mathieupommery/Keyring-GPSTRACKER/Docs/auxpcbside2.png

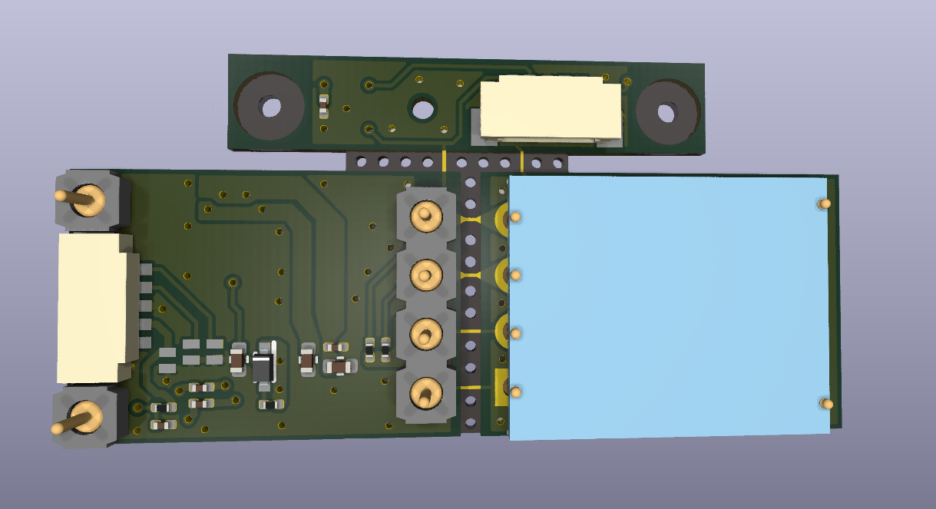
Docs/auxpcbside2.png
