mathieupommery/Keyring-GPSTRACKER/Docs/balise.jpeg

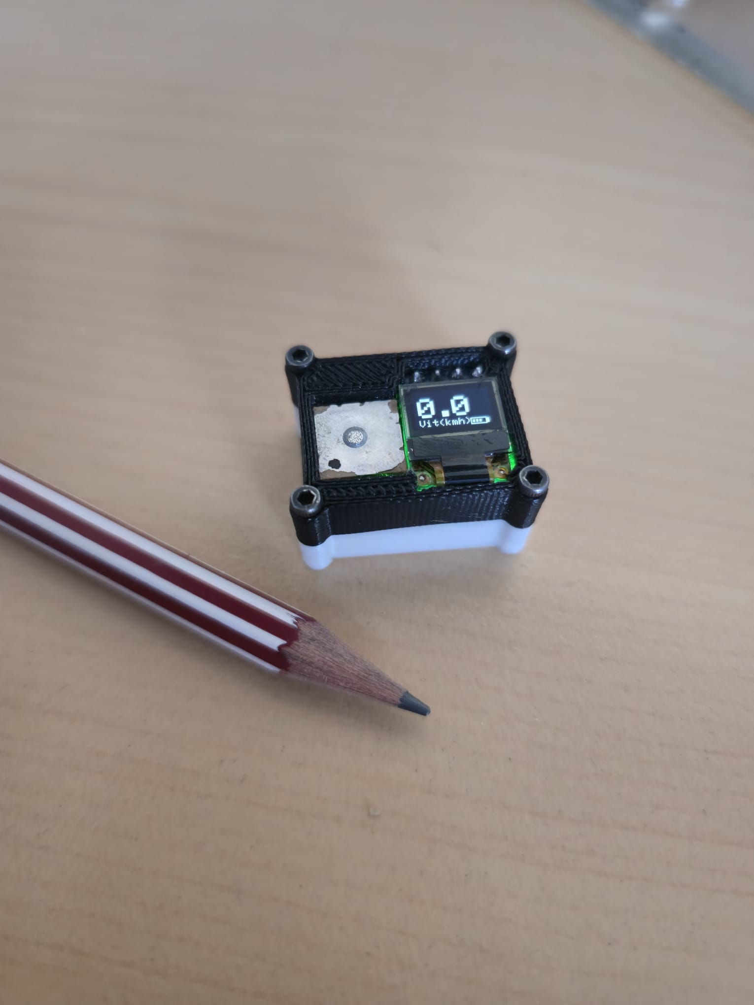
Docs/balise.jpeg
