mathieupommery/Keyring-GPSTRACKER/Docs/gpsbottom.png

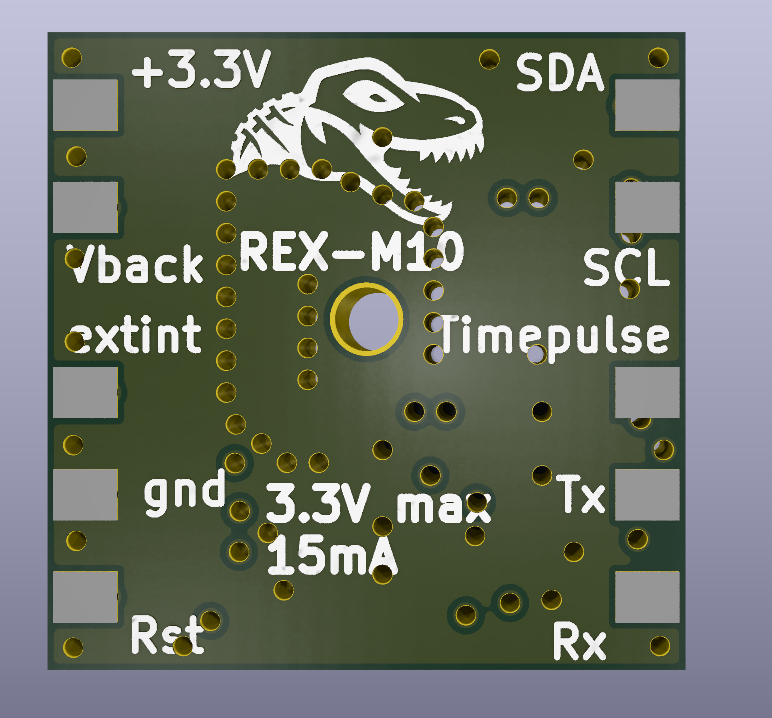
Docs/gpsbottom.png
