mathieupommery/Keyring-GPSTRACKER/Docs/rex_m10pcb.png

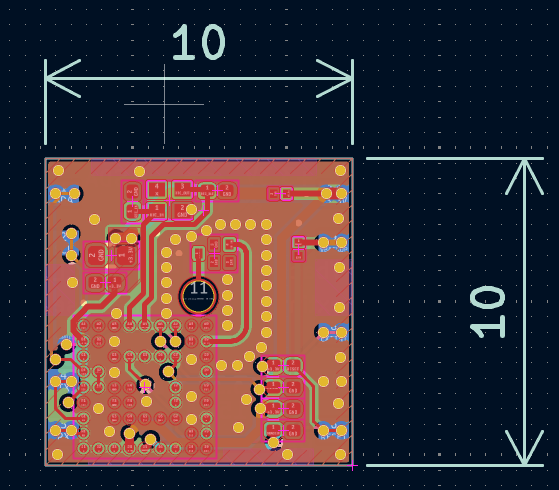
Docs/rex_m10pcb.png
