mathieupommery/Keyring-GPSTRACKER/Docs/v12back.png

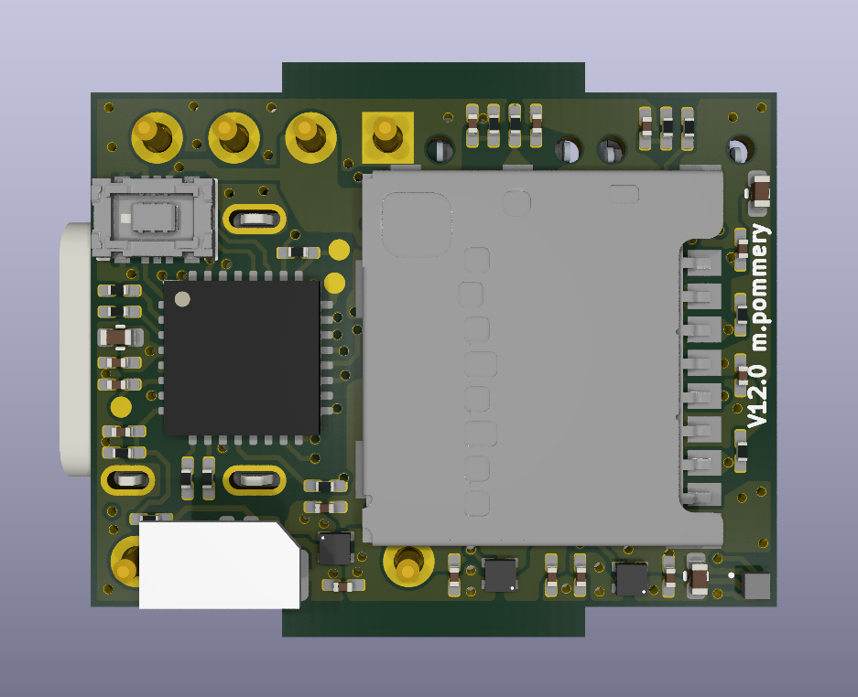
Docs/v12back.png
