mathieupommery/Keyring-GPSTRACKER/Docs/v12side.png

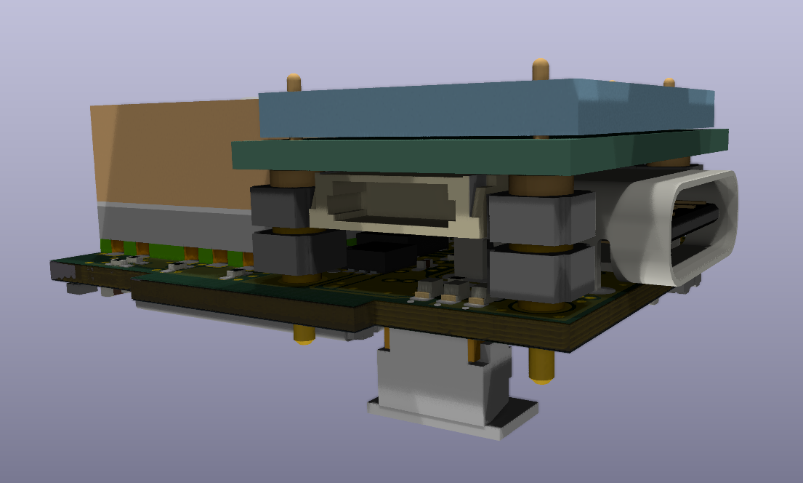
Docs/v12side.png
