mathieupommery/Keyring-GPSTRACKER/Docs/v12top.png

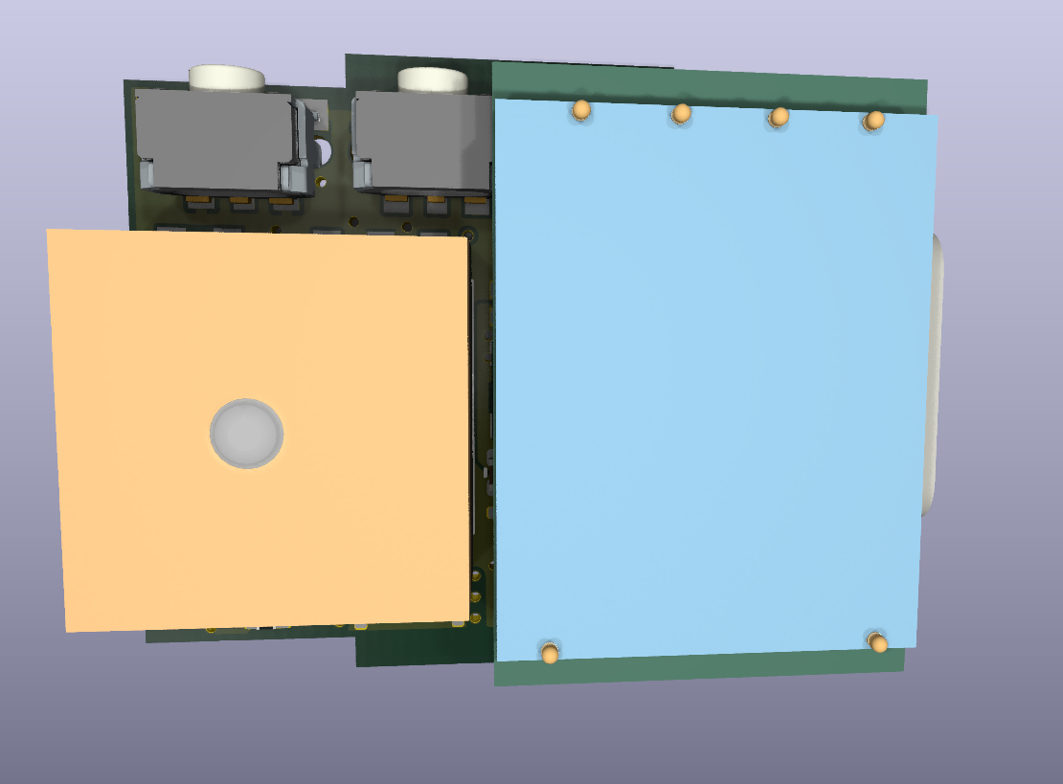
Docs/v12top.png
