mathieupommery/Keyring-GPSTRACKER/Docs/watercase1.png

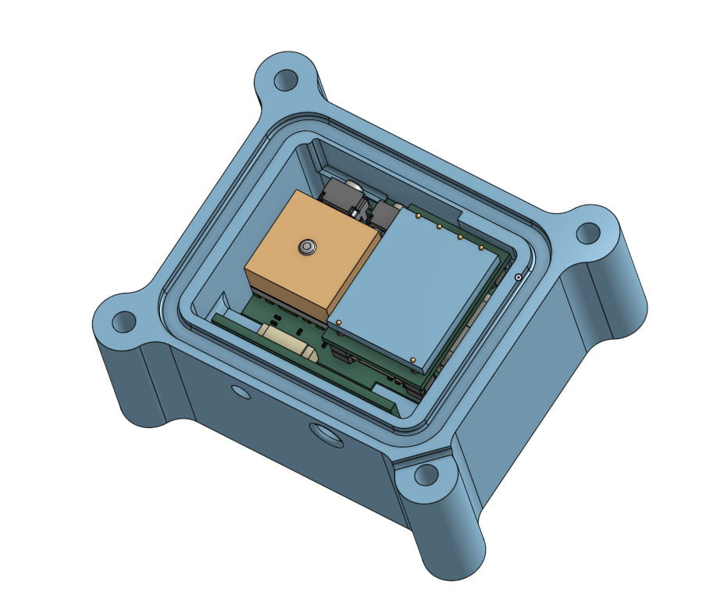
Docs/watercase1.png
