mathieupommery/Keyring-GPSTRACKER/Hardware/3d schématic/composant/BM06B-SURS-TF-LF--SN---3DModel-STEP-56544.STEP

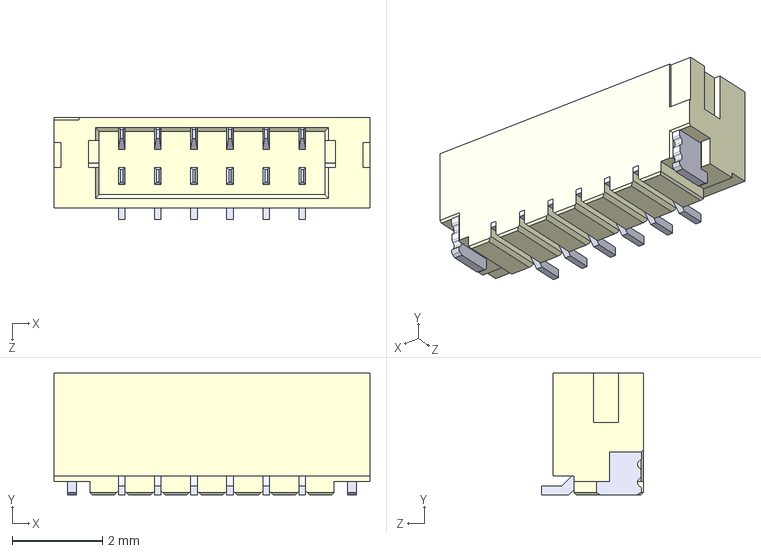
[picture p29: CAD file, 2026-07-01]
Hardware/3d schématic/composant/BM06B-SURS-TF-LF--SN---3DModel-STEP-56544.STEP
7.00 x 2.70 x 2.25 mm
