mathieupommery/Keyring-GPSTRACKER/Hardware/3d schématic/composant/0.42inch.step

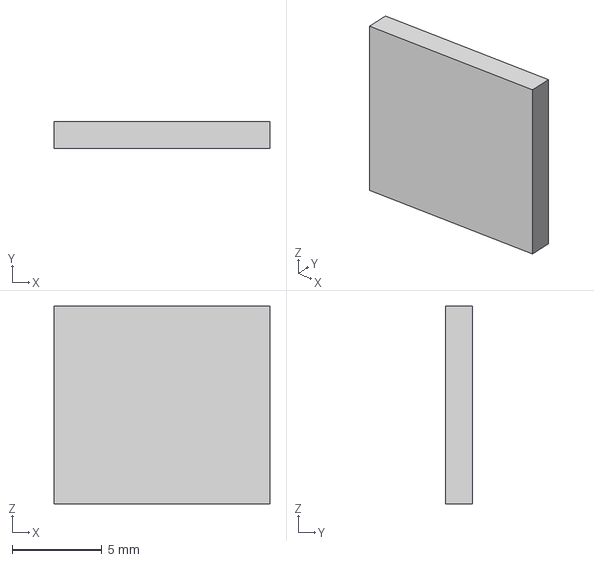
[picture p30: CAD file, 2026-07-01]
Hardware/3d schématic/composant/0.42inch.step
12.0 x 1.50 x 11.0 mm
