mathieupommery/Keyring-GPSTRACKER/Hardware/3d schématic/composant/CD-PA1010D--3DModel-STEP-271329.STEP

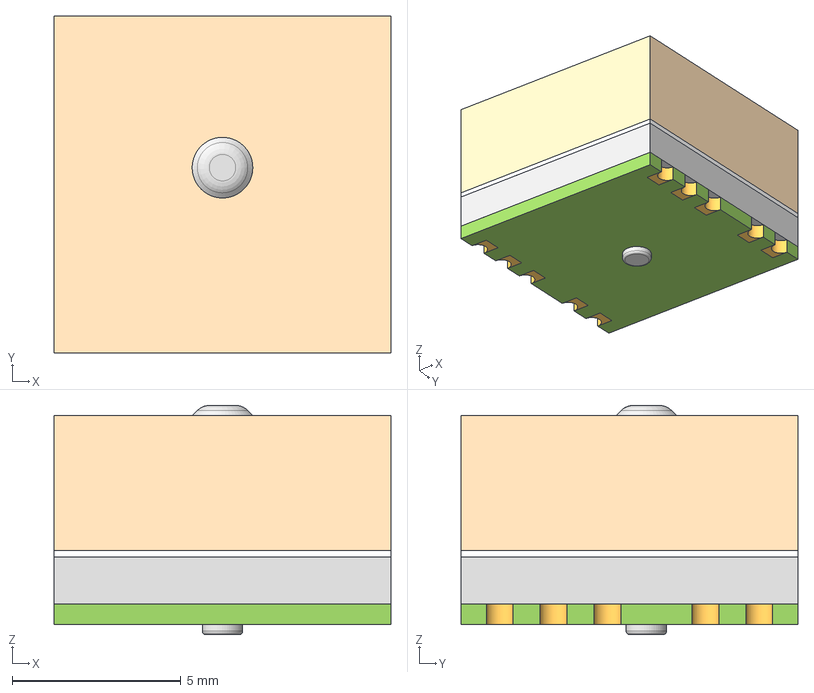
[picture p31: CAD file, 2024-11-02]
Hardware/3d schématic/composant/CD-PA1010D--3DModel-STEP-271329.STEP
10.0 x 10.0 x 6.80 mm
AntennaBottom
AntennaTop
BlockUp
Glue
BlockBottom
PCB
Pads
