mathieupommery/Keyring-GPSTRACKER/Hardware/3d schématic/composant/KXT321LHS.stp

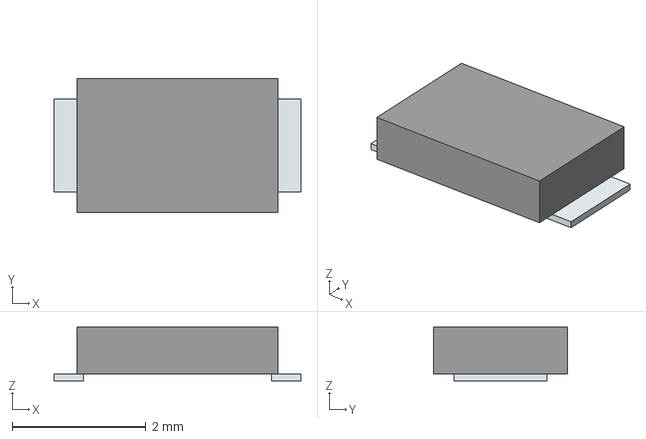
[picture p32: CAD file, 2024-11-02]
Hardware/3d schématic/composant/KXT321LHS.stp
3.69 x 2.00 x 0.8 mm
Pins
