mathieupommery/Keyring-GPSTRACKER/Hardware/3d schématic/composant/LTC4065AEDCPBF.stp

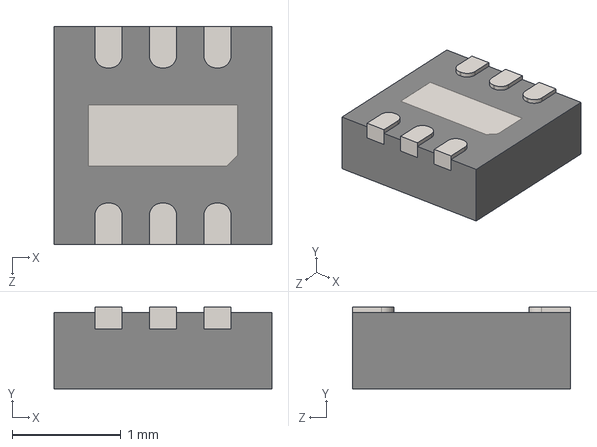
[picture p33: CAD file, 2024-11-02]
Hardware/3d schématic/composant/LTC4065AEDCPBF.stp
2.00 x 0.75 x 2.00 mm
