mathieupommery/Keyring-GPSTRACKER/Hardware/3d schématic/composant/LDLN025PU50R.stp

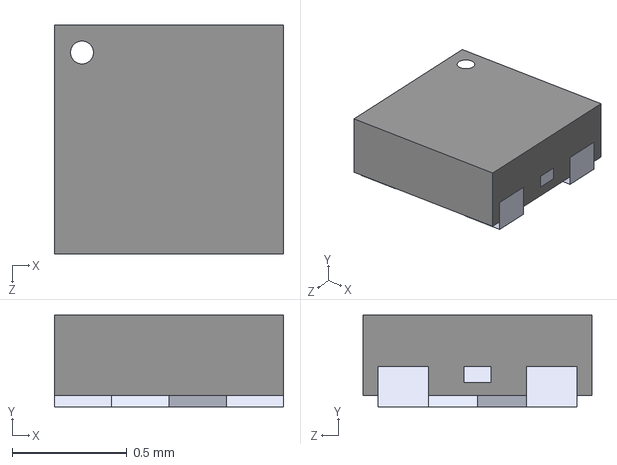
[picture p34: CAD file, 2024-06-09]
Hardware/3d schématic/composant/LDLN025PU50R.stp
1.00 x 0.4 x 1.00 mm
