mathieupommery/Keyring-GPSTRACKER/Software/Freertos_l432_v8/Core/Src/codeless_bin.c

#include <stdint.h>

const uint8_t codeless_bin[] = {
0x38,0x8d,0xfc,0x07,0x25,0x01,0xfc,0x07,0x2d,0x01,0xfc,0x07,
0x45,0x01,0xfc,0x07,0x00,0x00,0x00,0x00,0x00,0x00,0x00,0x00,
0x00,0x00,0x00,0x00,0x00,0x00,0x00,0x00,0x00,0x00,0x00,0x00,
0x00,0x00,0x00,0x00,0x00,0x00,0x00,0x00,0x5d,0x01,0xfc,0x07,
0x00,0x00,0x00,0x00,0x00,0x00,0x00,0x00,0x5f,0x01,0xfc,0x07,
0x61,0x01,0xfc,0x07,0x5d,0x0e,0xfc,0x07,0x4d,0x3a,0xfc,0x07,
0xa5,0x26,0xf0,0x07,0x63,0x01,0xfc,0x07,0x63,0x01,0xfc,0x07,
0x63,0x01,0xfc,0x07,0x21,0x0e,0xfc,0x07,0x63,0x01,0xfc,0x07,
0x2d,0x0e,0xfc,0x07,0x63,0x01,0xfc,0x07,0xe9,0x0e,0xfc,0x07,
0xf3,0x0e,0xfc,0x07,0xfd,0x0e,0xfc,0x07,0x07,0x0f,0xfc,0x07,
0x11,0x0f,0xfc,0x07,0x63,0x01,0xfc,0x07,0x19,0x11,0xfc,0x07,
0x63,0x01,0xfc,0x07,0x63,0x01,0xfc,0x07,0x63,0x01,0xfc,0x07,
0x63,0x01,0xfc,0x07,0x63,0x01,0xfc,0x07,0x63,0x01,0xfc,0x07,
0x63,0x01,0xfc,0x07,0x00,0x00,0x8e,0x07,0x0e,0x00,0x00,0x00,
0xff,0xff,0xff,0xff,0xff,0xff,0xff,0xff,0xff,0xff,0xff,0xff,
0xff,0xff,0xff,0xff,0xff,0xff,0xff,0xff,0xff,0xff,0xff,0xff,
0xff,0xff,0xff,0xff,0xff,0xff,0xff,0xff,0xff,0xff,0xff,0xff,
0xff,0xff,0xff,0xff,0xff,0xff,0xff,0xff,0xff,0xff,0xff,0xff,
0xff,0xff,0xff,0xff,0xff,0xff,0xff,0xff,0xff,0xff,0xff,0xff,
0xff,0xff,0xff,0xff,0xff,0xff,0xff,0xff,0xff,0xff,0xff,0xff,
0xff,0xff,0xff,0xff,0xff,0xff,0xff,0xff,0xff,0xff,0xff,0xff,
0xff,0xff,0xff,0xff,0xff,0xff,0xff,0xff,0xff,0xff,0xff,0xff,
0xff,0xff,0xff,0xff,0xff,0xff,0xff,0xff,0x03,0x48,0x85,0x46,
0x00,0xf0,0x62,0xfe,0x00,0x48,0x00,0x47,0xf1,0x29,0xfc,0x07,
0x38,0x8d,0xfc,0x07,0x0f,0x48,0x80,0x47,0x0f,0x48,0x00,0x47,
0x04,0x20,0x71,0x46,0x08,0x42,0x03,0xd0,0xef,0xf3,0x09,0x80,
0x0c,0x49,0x08,0x47,0xef,0xf3,0x08,0x80,0x0a,0x49,0x08,0x47,
0x04,0x20,0x71,0x46,0x08,0x42,0x03,0xd0,0xef,0xf3,0x09,0x80,
0x07,0x49,0x08,0x47,0xef,0xf3,0x08,0x80,0x05,0x49,0x08,0x47,
0xfe,0xe7,0xfe,0xe7,0xfe,0xe7,0xfe,0xe7,0x1d,0x76,0xfc,0x07,
0x11,0x01,0xfc,0x07,0x25,0x10,0xfc,0x07,0x0d,0x10,0xfc,0x07,
0xf8,0xb5,0x07,0x46,0x01,0x20,0x00,0x23,0x02,0x46,0x00,0x90,
0x19,0x46,0x03,0x20,0x49,0xf7,0x3e,0xf9,0x04,0x46,0x02,0x21,
0x80,0x30,0x01,0x70,0xfb,0x4d,0xfa,0x48,0x2a,0x68,0x43,0x88,
0x11,0x46,0xff,0x31,0xf7,0x31,0x0b,0x86,0x80,0x88,0x48,0x86,
0xf7,0x48,0x06,0x6a,0x01,0x23,0xdb,0x06,0x9e,0x43,0x1e,0x43,
0x06,0x62,0xff,0x32,0x00,0x20,0xff,0x32,0x38,0x32,0x50,0x82,
0x90,0x82,0xd0,0x82,0x1d,0x20,0x08,0x82,0xf0,0x48,0x48,0x84,
0xf0,0x48,0xc8,0x82,0xf0,0x48,0x08,0x83,0x00,0x20,0x48,0x82,
0x38,0x46,0x49,0xf7,0x55,0xfc,0x01,0x46,0x28,0x68,0xff,0x30,
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

};
const uint32_t codeless_bin_len = 36372;
