mathieupommery/Keyring-GPSTRACKER/Software/Freertos_l432_v8/Core/Src/screen_bitmaps.c

#include "screen_bitmaps.h"
#include "statemachine.h"

/* Bitmaps 64x32, format horizontal, MSB a gauche (byteWidth=8).
 Compatibles ssd1306_DrawBitmap. Remplacables via image2cpp (meme format). */

const uint8_t startimg[256] = { 0x00, 0x00, 0x00, 0x00, 0x00, 0x00, 0x00, 0x00,
		0x7f, 0xff, 0xff, 0xff, 0xff, 0xff, 0xff, 0xfe, 0x7f, 0xff, 0xff, 0xff,
		0xff, 0xff, 0xfe, 0x3e, 0x7f, 0xff, 0xff, 0xff, 0xff, 0xff, 0xf9, 0xce,
		0x7f, 0xff, 0xff, 0xff, 0xff, 0xff, 0xfa, 0x2e, 0x7f, 0xfc, 0x1f, 0xff,
		0xff, 0xff, 0xf6, 0xb6, 0x7f, 0xf0, 0x07, 0xff, 0xff, 0xff, 0xf6, 0x76,
		0x7f, 0xc0, 0x01, 0xff, 0xff, 0xff, 0xfa, 0xae, 0x7f, 0x80, 0x00, 0xff,
		0xff, 0xff, 0xf9, 0xce, 0x7f, 0x81, 0xc0, 0xff, 0xff, 0xff, 0xfe, 0x3e,
		0x7f, 0x03, 0xe0, 0x7f, 0xff, 0xff, 0xff, 0xfe, 0x7f, 0x07, 0xf0, 0x7f,
		0x0f, 0x03, 0xf0, 0x3e, 0x7f, 0x07, 0xf0, 0x7f, 0x0f, 0x03, 0xf0, 0x3e,
		0x7f, 0x07, 0xf0, 0x7c, 0xff, 0x3c, 0xcf, 0xfe, 0x7f, 0x03, 0xe0, 0x7c,
		0xff, 0x3c, 0xcf, 0xfe, 0x7f, 0x01, 0xc0, 0x7c, 0xc3, 0x03, 0xf0, 0xfe,
		0x7f, 0x80, 0x00, 0xfc, 0xc3, 0x03, 0xf0, 0xfe, 0x7f, 0x80, 0x00, 0xfc,
		0xf3, 0x3f, 0xff, 0x3e, 0x7f, 0xc0, 0x01, 0xfc, 0xf3, 0x3f, 0xff, 0x3e,
		0x7f, 0xc0, 0x01, 0xff, 0x0f, 0x3f, 0xc0, 0xfe, 0x7f, 0xe0, 0x03, 0xff,
		0x0f, 0x3f, 0xc0, 0xfe, 0x7f, 0xe0, 0x07, 0xff, 0xff, 0xff, 0xff, 0xfe,
		0x7f, 0xf0, 0x07, 0xff, 0xff, 0xff, 0xff, 0xfe, 0x7f, 0xf0, 0x0f, 0xff,
		0xff, 0x76, 0xfe, 0x7e, 0x7f, 0xf8, 0x0f, 0xff, 0xff, 0x74, 0xfd, 0xbe,
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

const uint8_t* ScreenAnim_GetBitmap(uint8_t state) {
	switch (state) {
	case STATE_SPEED:
		return bmp_speed;
	case STATE_BALISE:
		return bmp_balise;
	case STATE_POS:
		return bmp_pos;
	case STATE_CITY:
		return bmp_city;
	case STATE_SETTINGS:
		return bmp_settings;
	default:
		return 0;
	}
}
