mathieupommery/Keyring-GPSTRACKER/Software/freertos_msc/Core/Src/stm32wbxx_it.c

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

/* Includes ------------------------------------------------------------------*/
#include "main.h"
#include "stm32wbxx_it.h"
/* USER CODE BEGIN Includes */
#include "tim.h"
#include "ssd1306.h"
/* USER CODE END Includes */

/* USER CODE BEGIN PV */
extern int cptdoubledonnee;
extern int enablewrite;
extern uint16_t offsetforscroltext;
extern uint16_t scrolltextmax;
extern int bluetoothsend;
/* USER CODE END PV */

/* External variables --------------------------------------------------------*/
extern PCD_HandleTypeDef hpcd_USB_FS;
extern DMA_HandleTypeDef hdma_adc1;
extern IPCC_HandleTypeDef hipcc;
extern DMA_HandleTypeDef hdma_lpuart1_rx;
extern DMA_HandleTypeDef hdma_lpuart1_tx;
extern UART_HandleTypeDef hlpuart1;
extern RTC_HandleTypeDef hrtc;
extern TIM_HandleTypeDef htim16;
extern TIM_HandleTypeDef htim17;
extern TIM_HandleTypeDef htim1;

/******************************************************************************/
/*           Cortex Processor Interruption and Exception Handlers          */
/******************************************************************************/
/**
  * @brief This function handles Non maskable interrupt.
  */
void NMI_Handler(void)
{
  /* USER CODE BEGIN NonMaskableInt_IRQn 1 */
   while (1)
  {
	   ssd1306_SetCursor(32, 20);
	   	  ssd1306_WriteString("NMI", Font_7x10, White);
	   	  ssd1306_UpdateScreen();
  }
  /* USER CODE END NonMaskableInt_IRQn 1 */
}

/**
  * @brief This function handles Hard fault interrupt.
  */
void HardFault_Handler(void)
{
  while (1)
  {
    /* USER CODE BEGIN W1_HardFault_IRQn 0 */
	  ssd1306_SetCursor(32, 20);
	  ssd1306_WriteString("hardfault", Font_7x10, White);
	  ssd1306_UpdateScreen();
    /* USER CODE END W1_HardFault_IRQn 0 */
  }
}

/**
  * @brief This function handles Memory management fault.
  */
void MemManage_Handler(void)
{
  while (1)
  {
    /* USER CODE BEGIN W1_MemoryManagement_IRQn 0 */
	  ssd1306_SetCursor(32, 20);
	  	  ssd1306_WriteString("mem", Font_7x10, White);
	  	  ssd1306_UpdateScreen();
    /* USER CODE END W1_MemoryManagement_IRQn 0 */
  }
}

/**
  * @brief This function handles Prefetch fault, memory access fault.
  */
void BusFault_Handler(void)
{
  while (1)
  {
    /* USER CODE BEGIN W1_BusFault_IRQn 0 */
	  ssd1306_SetCursor(32, 20);
	  	  ssd1306_WriteString("bus", Font_7x10, White);
	  	  ssd1306_UpdateScreen();
    /* USER CODE END W1_BusFault_IRQn 0 */
  }
}

/**
  * @brief This function handles Undefined instruction or illegal state.
  */
void UsageFault_Handler(void)
{
  while (1)
  {
    /* USER CODE BEGIN W1_UsageFault_IRQn 0 */
	  ssd1306_SetCursor(32, 20);
	  	  ssd1306_WriteString("usage", Font_7x10, White);
	  	  ssd1306_UpdateScreen();
    /* USER CODE END W1_UsageFault_IRQn 0 */
  }
}

/**
  * @brief This function handles Debug monitor.
  */
void DebugMon_Handler(void)
{
}

/******************************************************************************/
/* STM32WBxx Peripheral Interrupt Handlers                                    */
/* Add here the Interrupt Handlers for the used peripherals.                  */
/* For the available peripheral interrupt handler names,                      */
/* please refer to the startup file (startup_stm32wbxx.s).                    */
/******************************************************************************/

/**
  * @brief This function handles RTC wake-up interrupt through EXTI line 19.
  */
void RTC_WKUP_IRQHandler(void)
{
  HAL_RTCEx_WakeUpTimerIRQHandler(&hrtc);
}

/**
  * @brief This function handles DMA1 channel1 global interrupt.
  */
void DMA1_Channel1_IRQHandler(void)
{
  HAL_DMA_IRQHandler(&hdma_adc1);
}

/**
  * @brief This function handles DMA1 channel2 global interrupt.
  */
void DMA1_Channel2_IRQHandler(void)
{
  HAL_DMA_IRQHandler(&hdma_lpuart1_rx);
}

/**
  * @brief This function handles DMA1 channel3 global interrupt.
  */
void DMA1_Channel3_IRQHandler(void)
{
  HAL_DMA_IRQHandler(&hdma_lpuart1_tx);
}

/**
  * @brief This function handles USB low priority interrupt, USB wake-up interrupt through EXTI line 28.
  */
void USB_LP_IRQHandler(void)
{
  HAL_PCD_IRQHandler(&hpcd_USB_FS);
}

/**
  * @brief This function handles EXTI line[9:5] interrupts.
  */
void EXTI9_5_IRQHandler(void)
{
  HAL_GPIO_EXTI_IRQHandler(GPIO_PIN_9);
}

/**
  * @brief This function handles TIM1 update interrupt and TIM16 global interrupt.
  */
void TIM1_UP_TIM16_IRQHandler(void)
{
  if (htim1.Instance != NULL)
  {
    HAL_TIM_IRQHandler(&htim1);
  }
  if (htim16.Instance != NULL)
  {
    HAL_TIM_IRQHandler(&htim16);
  }
}

/**
  * @brief This function handles TIM1 trigger and commutation interrupts and TIM17 global interrupt.
  */
void TIM1_TRG_COM_TIM17_IRQHandler(void)
{
  HAL_TIM_IRQHandler(&htim17);
}

/**
  * @brief This function handles LPUART1 global interrupt.
  */
void LPUART1_IRQHandler(void)
{
  HAL_UART_IRQHandler(&hlpuart1);
}

/**
  * @brief This function handles EXTI line[15:10] interrupts.
  */
void EXTI15_10_IRQHandler(void)
{
  HAL_GPIO_EXTI_IRQHandler(GPIO_PIN_14);
  HAL_GPIO_EXTI_IRQHandler(GPIO_PIN_15);
}

/**
  * @brief This function handles IPCC RX occupied interrupt.
  */
void IPCC_C1_RX_IRQHandler(void)
{
  HAL_IPCC_RX_IRQHandler(&hipcc);
}

/**
  * @brief This function handles IPCC TX free interrupt.
  */
void IPCC_C1_TX_IRQHandler(void)
{
  HAL_IPCC_TX_IRQHandler(&hipcc);
}

/**
  * @brief This function handles HSEM global interrupt.
  */
void HSEM_IRQHandler(void)
{
  HAL_HSEM_IRQHandler();
}
