mathieupommery/Keyring-GPSTRACKER/Software/freertos_msc/Core/Src/tim.c

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
/* Includes ------------------------------------------------------------------*/
#include "tim.h"

/* USER CODE BEGIN 0 */
extern uint8_t SEC;
extern uint8_t HR;
extern uint8_t MINUTE;
extern uint8_t JOURS;
extern uint8_t MOIS;
extern uint16_t ANNEE;
extern MOIS_STATE mois;
/* USER CODE END 0 */

TIM_HandleTypeDef htim2;
TIM_HandleTypeDef htim16;
TIM_HandleTypeDef htim17;

/* TIM2 init function */
void MX_TIM2_Init(void)
{

  TIM_ClockConfigTypeDef sClockSourceConfig = {0};
  TIM_MasterConfigTypeDef sMasterConfig = {0};

  htim2.Instance = TIM2;
  htim2.Init.Prescaler = 6400-1;
  htim2.Init.CounterMode = TIM_COUNTERMODE_UP;
  htim2.Init.Period = 1000-1;
  htim2.Init.ClockDivision = TIM_CLOCKDIVISION_DIV1;
  htim2.Init.AutoReloadPreload = TIM_AUTORELOAD_PRELOAD_DISABLE;
  if (HAL_TIM_Base_Init(&htim2) != HAL_OK)
  {
    Error_Handler();
  }
  sClockSourceConfig.ClockSource = TIM_CLOCKSOURCE_INTERNAL;
  if (HAL_TIM_ConfigClockSource(&htim2, &sClockSourceConfig) != HAL_OK)
  {
    Error_Handler();
  }
  sMasterConfig.MasterOutputTrigger = TIM_TRGO_UPDATE;
  sMasterConfig.MasterSlaveMode = TIM_MASTERSLAVEMODE_DISABLE;
  if (HAL_TIMEx_MasterConfigSynchronization(&htim2, &sMasterConfig) != HAL_OK)
  {
    Error_Handler();
  }
}
/* TIM16 init function */
void MX_TIM16_Init(void)
{

  htim16.Instance = TIM16;
  htim16.Init.Prescaler = 64000-1;
  htim16.Init.CounterMode = TIM_COUNTERMODE_UP;
  htim16.Init.Period = 65535;
  htim16.Init.ClockDivision = TIM_CLOCKDIVISION_DIV1;
  htim16.Init.RepetitionCounter = 0;
  htim16.Init.AutoReloadPreload = TIM_AUTORELOAD_PRELOAD_DISABLE;
  if (HAL_TIM_Base_Init(&htim16) != HAL_OK)
  {
    Error_Handler();
  }
}
/* TIM17 init function */
void MX_TIM17_Init(void)
{

  htim17.Instance = TIM17;
  htim17.Init.Prescaler = 64000-1;
  htim17.Init.CounterMode = TIM_COUNTERMODE_UP;
  htim17.Init.Period = 200-1;
  htim17.Init.ClockDivision = TIM_CLOCKDIVISION_DIV1;
  htim17.Init.RepetitionCounter = 0;
  htim17.Init.AutoReloadPreload = TIM_AUTORELOAD_PRELOAD_DISABLE;
  if (HAL_TIM_Base_Init(&htim17) != HAL_OK)
  {
    Error_Handler();
  }
}

void HAL_TIM_Base_MspInit(TIM_HandleTypeDef* tim_baseHandle)
{

  if(tim_baseHandle->Instance==TIM2)
  {
    /* TIM2 clock enable */
    __HAL_RCC_TIM2_CLK_ENABLE();
  }
  else if(tim_baseHandle->Instance==TIM16)
  {
    /* TIM16 clock enable */
    __HAL_RCC_TIM16_CLK_ENABLE();

    /* TIM16 interrupt Init */
    HAL_NVIC_SetPriority(TIM1_UP_TIM16_IRQn, 15, 0);
    HAL_NVIC_EnableIRQ(TIM1_UP_TIM16_IRQn);
  }
  else if(tim_baseHandle->Instance==TIM17)
  {
    /* TIM17 clock enable */
    __HAL_RCC_TIM17_CLK_ENABLE();

    /* TIM17 interrupt Init */
    HAL_NVIC_SetPriority(TIM1_TRG_COM_TIM17_IRQn, 5, 0);
    HAL_NVIC_EnableIRQ(TIM1_TRG_COM_TIM17_IRQn);
  }
}

void HAL_TIM_Base_MspDeInit(TIM_HandleTypeDef* tim_baseHandle)
{

  if(tim_baseHandle->Instance==TIM2)
  {
    /* Peripheral clock disable */
    __HAL_RCC_TIM2_CLK_DISABLE();
  }
  else if(tim_baseHandle->Instance==TIM16)
  {
    /* Peripheral clock disable */
    __HAL_RCC_TIM16_CLK_DISABLE();

    /* TIM16 interrupt Deinit */
    HAL_NVIC_DisableIRQ(TIM1_UP_TIM16_IRQn);
  }
  else if(tim_baseHandle->Instance==TIM17)
  {
    /* Peripheral clock disable */
    __HAL_RCC_TIM17_CLK_DISABLE();

    /* TIM17 interrupt Deinit */
    HAL_NVIC_DisableIRQ(TIM1_TRG_COM_TIM17_IRQn);
  }
}

/* USER CODE BEGIN 1 */
void updatedate(void){

	SEC+=1;
	if(SEC>59){
		SEC=0;
		MINUTE+=1;
	}

	if(MINUTE>59){

		MINUTE=0;
		HR+=1;
	}
	if(HR>=24){
		HR=0;
		JOURS+=1;
	}
	switch (mois){

	case JANVIER:
		if(JOURS>31){
			JOURS=1;
			mois++;
			MOIS++;
		}

		break;
	case FEVRIER:
		if(JOURS>29){
					JOURS=1;
					mois++;
					MOIS++;
				}
		break;
	case MARS:
		if(JOURS>31){
					JOURS=1;
					mois++;
					MOIS++;
				}
		break;
	case AVRIL:
		if(JOURS>30){
					JOURS=1;
					mois++;
					MOIS++;
				}
		break;
	case MAI:
		if(JOURS>31){
					JOURS=1;
					mois++;
					MOIS++;
				}
		break;
	case JUIN:
		if(JOURS>30){
					JOURS=1;
					mois++;
					MOIS++;
				}
		break;
	case JUILLET:
		if(JOURS>31){
					JOURS=1;
					mois++;
					MOIS++;
				}
		break;
	case AOUT:
		if(JOURS>31){
					JOURS=1;
					mois++;
					MOIS++;
				}
		break;
	case SEPTEMBRE:
		if(JOURS>30){
					JOURS=1;
					mois++;
					MOIS++;
				}
		break;
	case OCTOBRE:
		if(JOURS>31){
					JOURS=1;
					mois++;
					MOIS++;
				}
		break;
	case NOVEMBRE:
		if(JOURS>30){
					JOURS=1;
					mois++;
					MOIS++;
				}
		break;
	case DECEMBRE:
		if(JOURS>31){
					JOURS=1;
					mois++;
					MOIS++;
				}
		break;

	}

	if(MOIS>12){
		mois=JANVIER;
		MOIS=1;
		ANNEE++;
	}
}
/* USER CODE END 1 */
