mathieupommery/Keyring-GPSTRACKER/Software/freertos_msc/Core/Src/usart.c

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
/* Includes ------------------------------------------------------------------*/
#include "usart.h"

/* USER CODE BEGIN 0 */
#include "GNSS.h"

extern uint8_t workingbuffer[110];
extern GNSS_StateHandle GNSSData;
extern int received_flag;
int timetest1=0;
int timetest2=0;
int itest=0;
/* USER CODE END 0 */

UART_HandleTypeDef hlpuart1;
DMA_HandleTypeDef hdma_lpuart1_rx;
DMA_HandleTypeDef hdma_lpuart1_tx;

/* LPUART1 init function */

void MX_LPUART1_UART_Init(void)
{

  hlpuart1.Instance = LPUART1;
  hlpuart1.Init.BaudRate = 115200;
  hlpuart1.Init.WordLength = UART_WORDLENGTH_8B;
  hlpuart1.Init.StopBits = UART_STOPBITS_1;
  hlpuart1.Init.Parity = UART_PARITY_NONE;
  hlpuart1.Init.Mode = UART_MODE_TX_RX;
  hlpuart1.Init.HwFlowCtl = UART_HWCONTROL_NONE;
  hlpuart1.Init.OneBitSampling = UART_ONE_BIT_SAMPLE_DISABLE;
  hlpuart1.Init.ClockPrescaler = UART_PRESCALER_DIV1;
  hlpuart1.AdvancedInit.AdvFeatureInit = UART_ADVFEATURE_NO_INIT;
  hlpuart1.FifoMode = UART_FIFOMODE_DISABLE;
  if (HAL_UART_Init(&hlpuart1) != HAL_OK)
  {
    Error_Handler();
  }
  if (HAL_UARTEx_SetTxFifoThreshold(&hlpuart1, UART_TXFIFO_THRESHOLD_1_8) != HAL_OK)
  {
    Error_Handler();
  }
  if (HAL_UARTEx_SetRxFifoThreshold(&hlpuart1, UART_RXFIFO_THRESHOLD_1_8) != HAL_OK)
  {
    Error_Handler();
  }
  if (HAL_UARTEx_DisableFifoMode(&hlpuart1) != HAL_OK)
  {
    Error_Handler();
  }
}

void HAL_UART_MspInit(UART_HandleTypeDef* uartHandle)
{

  GPIO_InitTypeDef GPIO_InitStruct = {0};
  RCC_PeriphCLKInitTypeDef PeriphClkInitStruct = {0};
  if(uartHandle->Instance==LPUART1)
  {
  /** Initializes the peripherals clock
  */
    PeriphClkInitStruct.PeriphClockSelection = RCC_PERIPHCLK_LPUART1;
    PeriphClkInitStruct.Lpuart1ClockSelection = RCC_LPUART1CLKSOURCE_HSI;
    if (HAL_RCCEx_PeriphCLKConfig(&PeriphClkInitStruct) != HAL_OK)
    {
      Error_Handler();
    }

    /* LPUART1 clock enable */
    __HAL_RCC_LPUART1_CLK_ENABLE();

    __HAL_RCC_GPIOA_CLK_ENABLE();
    /**LPUART1 GPIO Configuration
    PA2     ------> LPUART1_TX
    PA3     ------> LPUART1_RX
    */
    GPIO_InitStruct.Pin = GPIO_PIN_2|GPIO_PIN_3;
    GPIO_InitStruct.Mode = GPIO_MODE_AF_PP;
    GPIO_InitStruct.Pull = GPIO_NOPULL;
    GPIO_InitStruct.Speed = GPIO_SPEED_FREQ_LOW;
    GPIO_InitStruct.Alternate = GPIO_AF8_LPUART1;
    HAL_GPIO_Init(GPIOA, &GPIO_InitStruct);

    /* LPUART1 DMA Init */
    /* LPUART1_RX Init */
    hdma_lpuart1_rx.Instance = DMA1_Channel2;
    hdma_lpuart1_rx.Init.Request = DMA_REQUEST_LPUART1_RX;
    hdma_lpuart1_rx.Init.Direction = DMA_PERIPH_TO_MEMORY;
    hdma_lpuart1_rx.Init.PeriphInc = DMA_PINC_DISABLE;
    hdma_lpuart1_rx.Init.MemInc = DMA_MINC_ENABLE;
    hdma_lpuart1_rx.Init.PeriphDataAlignment = DMA_PDATAALIGN_BYTE;
    hdma_lpuart1_rx.Init.MemDataAlignment = DMA_MDATAALIGN_BYTE;
    hdma_lpuart1_rx.Init.Mode = DMA_CIRCULAR;
    hdma_lpuart1_rx.Init.Priority = DMA_PRIORITY_LOW;
    if (HAL_DMA_Init(&hdma_lpuart1_rx) != HAL_OK)
    {
      Error_Handler();
    }

    __HAL_LINKDMA(uartHandle,hdmarx,hdma_lpuart1_rx);

    /* LPUART1_TX Init */
    hdma_lpuart1_tx.Instance = DMA1_Channel3;
    hdma_lpuart1_tx.Init.Request = DMA_REQUEST_LPUART1_TX;
    hdma_lpuart1_tx.Init.Direction = DMA_MEMORY_TO_PERIPH;
    hdma_lpuart1_tx.Init.PeriphInc = DMA_PINC_DISABLE;
    hdma_lpuart1_tx.Init.MemInc = DMA_MINC_ENABLE;
    hdma_lpuart1_tx.Init.PeriphDataAlignment = DMA_PDATAALIGN_BYTE;
    hdma_lpuart1_tx.Init.MemDataAlignment = DMA_MDATAALIGN_BYTE;
    hdma_lpuart1_tx.Init.Mode = DMA_NORMAL;
    hdma_lpuart1_tx.Init.Priority = DMA_PRIORITY_LOW;
    if (HAL_DMA_Init(&hdma_lpuart1_tx) != HAL_OK)
    {
      Error_Handler();
    }

    __HAL_LINKDMA(uartHandle,hdmatx,hdma_lpuart1_tx);

    /* LPUART1 interrupt Init */
    HAL_NVIC_SetPriority(LPUART1_IRQn, 6, 0);
    HAL_NVIC_EnableIRQ(LPUART1_IRQn);
  }
}

void HAL_UART_MspDeInit(UART_HandleTypeDef* uartHandle)
{

  if(uartHandle->Instance==LPUART1)
  {
    /* Peripheral clock disable */
    __HAL_RCC_LPUART1_CLK_DISABLE();

    /**LPUART1 GPIO Configuration
    PA2     ------> LPUART1_TX
    PA3     ------> LPUART1_RX
    */
    HAL_GPIO_DeInit(GPIOA, GPIO_PIN_2|GPIO_PIN_3);

    /* LPUART1 DMA DeInit */
    HAL_DMA_DeInit(uartHandle->hdmarx);
    HAL_DMA_DeInit(uartHandle->hdmatx);

    /* LPUART1 interrupt Deinit */
    HAL_NVIC_DisableIRQ(LPUART1_IRQn);
  }
}

/* USER CODE BEGIN 1 */
void HAL_UART_RxCpltCallback(UART_HandleTypeDef *huart){
	if(huart->Instance==LPUART1){
		if(itest==0){
			timetest1=HAL_GetTick();
		}
		itest++;
		if(itest>=10){
			itest=0;
			timetest2=HAL_GetTick()-timetest1;




		}
		received_flag=1;
		memcpy((uint8_t*)GNSSData.uartWorkingBuffer,(uint8_t *) workingbuffer,100);
		__HAL_DMA_DISABLE_IT(&hdma_lpuart1_rx, DMA_IT_HT);
		HAL_UART_Receive_DMA(&hlpuart1, (uint8_t *)workingbuffer, 100);

	}

}








/* USER CODE END 1 */
