mathieupommery/Keyring-GPSTRACKER/Software/freertos_msc_wb55ce/Core/Src/rtc.c

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
/* Includes ------------------------------------------------------------------*/
#include "rtc.h"

/* USER CODE BEGIN 0 */
extern uint8_t SEC;
extern uint8_t HR;
extern uint8_t MINUTE;
extern uint8_t JOURS;
extern uint8_t MOIS;
extern uint16_t ANNEE;
/* USER CODE END 0 */

RTC_HandleTypeDef hrtc;

/* RTC init function */
void MX_RTC_Init(void)
{

  RTC_TimeTypeDef sTime = {0};
  RTC_DateTypeDef sDate = {0};

  /** Initialize RTC Only
  */
  hrtc.Instance = RTC;
  hrtc.Init.HourFormat = RTC_HOURFORMAT_24;
  hrtc.Init.AsynchPrediv = 99;
  hrtc.Init.SynchPrediv = 9999;
  hrtc.Init.OutPut = RTC_OUTPUT_DISABLE;
  hrtc.Init.OutPutPolarity = RTC_OUTPUT_POLARITY_HIGH;
  hrtc.Init.OutPutType = RTC_OUTPUT_TYPE_OPENDRAIN;
  hrtc.Init.OutPutRemap = RTC_OUTPUT_REMAP_NONE;
  if (HAL_RTC_Init(&hrtc) != HAL_OK)
  {
    Error_Handler();
  }

  /** Initialize RTC and set the Time and Date
  */
  sTime.Hours = 0x0;
  sTime.Minutes = 0x0;
  sTime.Seconds = 0x0;
  sTime.SubSeconds = 0x0;
  sTime.DayLightSaving = RTC_DAYLIGHTSAVING_NONE;
  sTime.StoreOperation = RTC_STOREOPERATION_RESET;
  if (HAL_RTC_SetTime(&hrtc, &sTime, RTC_FORMAT_BCD) != HAL_OK)
  {
    Error_Handler();
  }
  sDate.WeekDay = RTC_WEEKDAY_MONDAY;
  sDate.Month = RTC_MONTH_JANUARY;
  sDate.Date = 0x1;
  sDate.Year = 0x0;

  if (HAL_RTC_SetDate(&hrtc, &sDate, RTC_FORMAT_BCD) != HAL_OK)
  {
    Error_Handler();
  }
}

void HAL_RTC_MspInit(RTC_HandleTypeDef* rtcHandle)
{

  RCC_PeriphCLKInitTypeDef PeriphClkInitStruct = {0};
  if(rtcHandle->Instance==RTC)
  {
  /** Initializes the peripherals clock
  */
    PeriphClkInitStruct.PeriphClockSelection = RCC_PERIPHCLK_RTC;
    PeriphClkInitStruct.RTCClockSelection = RCC_RTCCLKSOURCE_HSE_DIV32;
    if (HAL_RCCEx_PeriphCLKConfig(&PeriphClkInitStruct) != HAL_OK)
    {
      Error_Handler();
    }

    /* RTC clock enable */
    __HAL_RCC_RTC_ENABLE();
    __HAL_RCC_RTCAPB_CLK_ENABLE();
  }
}

void HAL_RTC_MspDeInit(RTC_HandleTypeDef* rtcHandle)
{

  if(rtcHandle->Instance==RTC)
  {
    /* Peripheral clock disable */
    __HAL_RCC_RTC_DISABLE();
    __HAL_RCC_RTCAPB_CLK_DISABLE();
  }
}

/* USER CODE BEGIN 1 */
void set_time (uint8_t hr, uint8_t min, uint8_t sec)
{
	RTC_TimeTypeDef sTime = {0};
	sTime.Hours = hr;
	sTime.Minutes = min;
	sTime.Seconds = sec;
	sTime.DayLightSaving = RTC_DAYLIGHTSAVING_NONE;
	sTime.StoreOperation = RTC_STOREOPERATION_RESET;
	if (HAL_RTC_SetTime(&hrtc, &sTime, RTC_FORMAT_BIN) != HAL_OK)
	{
		Error_Handler();
	}
}

void set_date (uint8_t year, uint8_t month, uint8_t date, uint8_t day)  // monday = 1
{
	RTC_DateTypeDef sDate = {0};
	sDate.WeekDay = day;
	sDate.Month = month;
	sDate.Date = date;
	sDate.Year = year;
	if (HAL_RTC_SetDate(&hrtc, &sDate, RTC_FORMAT_BIN) != HAL_OK)
	{
		Error_Handler();
	}

	HAL_RTCEx_BKUPWrite(&hrtc, RTC_BKP_DR1, 0x2345);  // backup register
}


void get_time_date()
{
  RTC_DateTypeDef gDate;
  RTC_TimeTypeDef gTime;

  /* Get the RTC current Time */
  HAL_RTC_GetTime(&hrtc, &gTime, RTC_FORMAT_BIN);
  /* Get the RTC current Date */
  HAL_RTC_GetDate(&hrtc, &gDate, RTC_FORMAT_BIN);

  SEC=gTime.Seconds;
  HR=gTime.Hours;
  MINUTE=gTime.Minutes;
  JOURS=gDate.Date;
  MOIS=gDate.Month;
  ANNEE=gDate.Year+2000;

  /* Display time Format: hh:mm:ss */
  //sprintf((char*)time,"%02d:%02d:%02d",gTime.Hours, gTime.Minutes, gTime.Seconds);

  /* Display date Format: dd-mm-yyyy */
  //sprintf((char*)date,"%02d-%02d-%2d",gDate.Date, gDate.Month, 2000 + gDate.Year);
}
/* USER CODE END 1 */
